TECHOTAKU182/Pilot-Light/enclosure/previews/dimensions.png

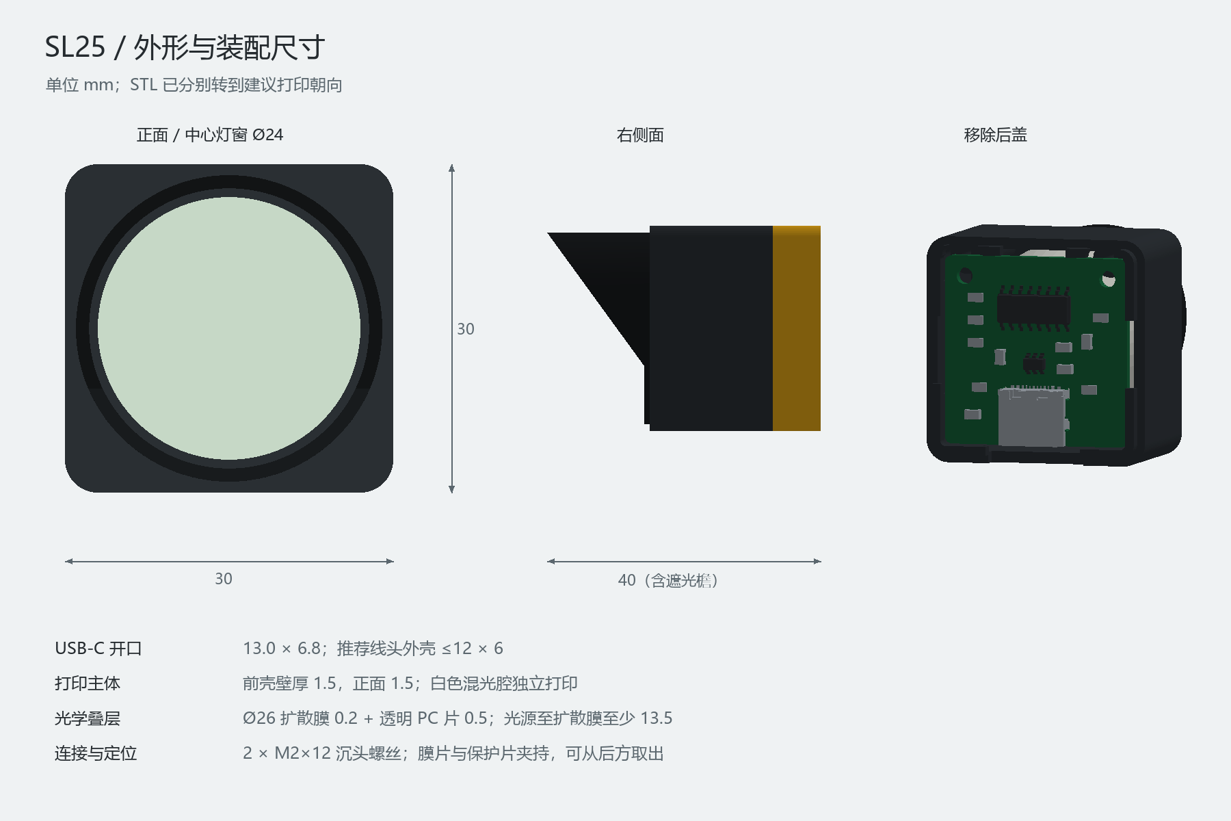
enclosure/previews/dimensions.png
