TECHOTAKU182/Pilot-Light/enclosure/previews/hood_profile.png

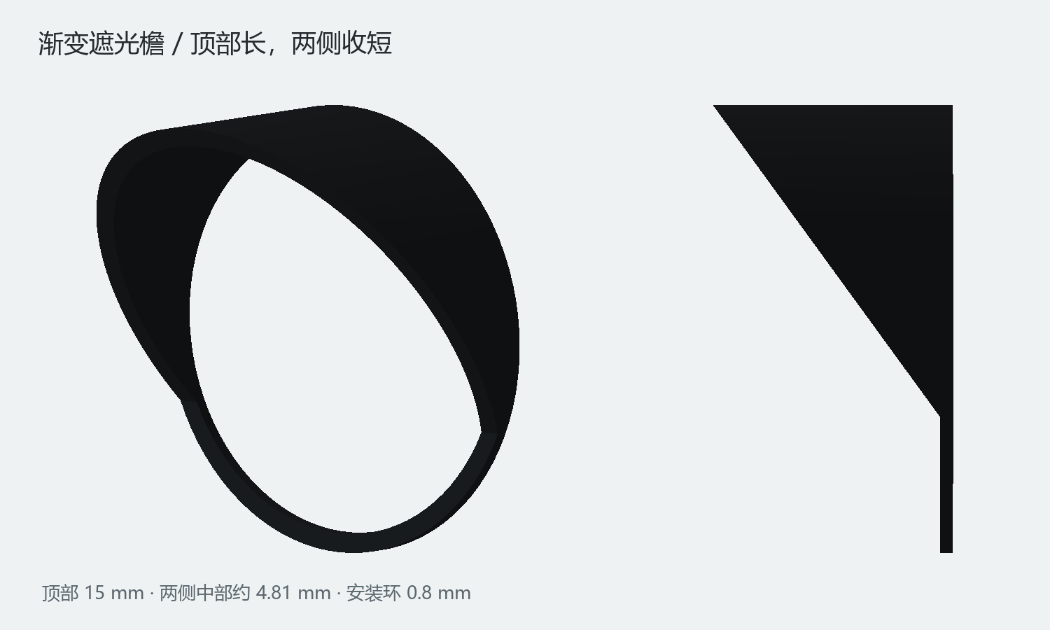
enclosure/previews/hood_profile.png
