TECHOTAKU182/Pilot-Light/enclosure/sl25_traffic/preview/color_states.png

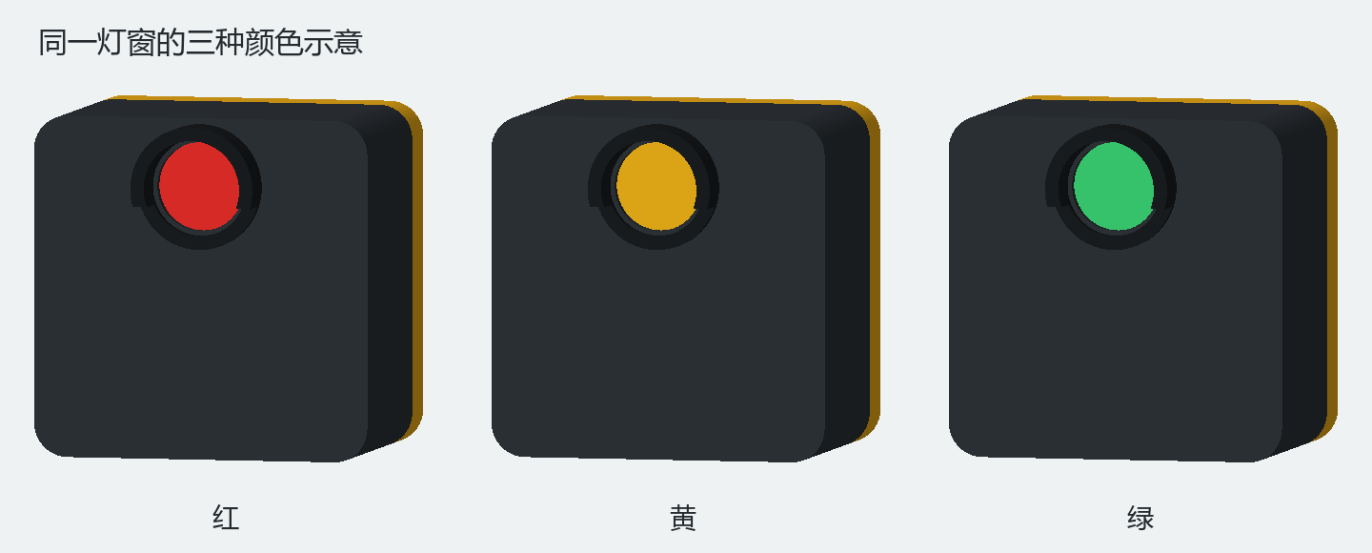
enclosure/sl25_traffic/preview/color_states.png
