TECHOTAKU182/Pilot-Light/enclosure/sl25_traffic/preview/dimensions.png

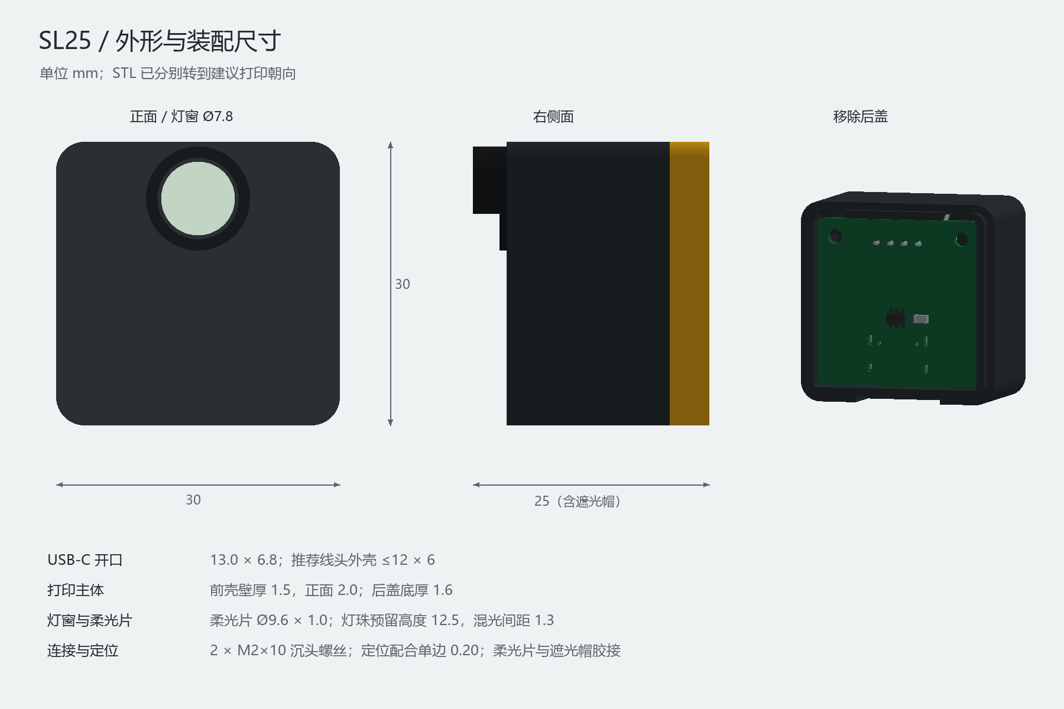
enclosure/sl25_traffic/preview/dimensions.png
