TECHOTAKU182/Pilot-Light/enclosure/sl25_traffic/preview/usb_underside.png

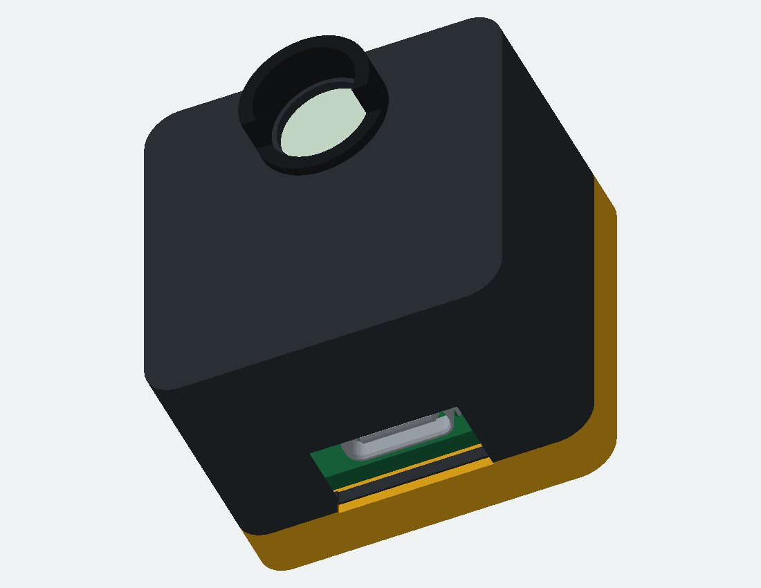
enclosure/sl25_traffic/preview/usb_underside.png
