TECHOTAKU182/Pilot-Light/enclosure/sl25_traffic_rev_b/preview/color_states.png

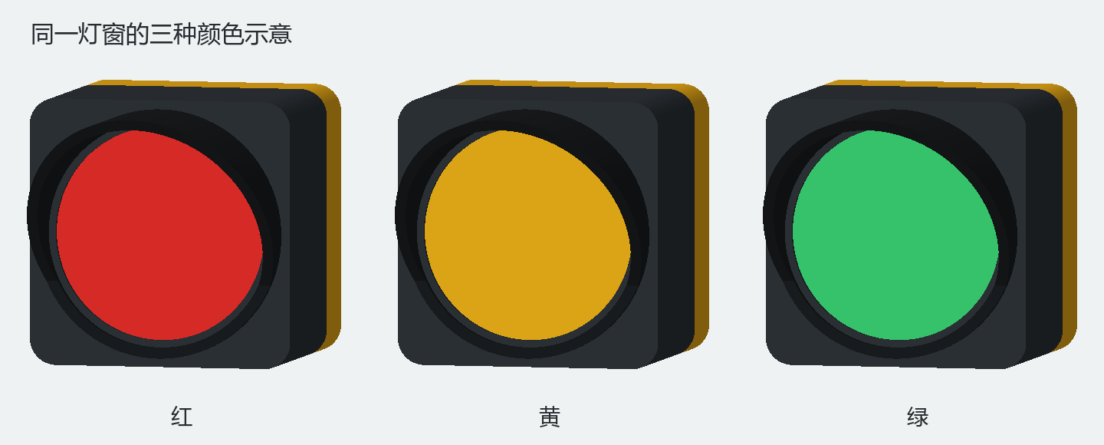
enclosure/sl25_traffic_rev_b/preview/color_states.png
