TECHOTAKU182/Pilot-Light/enclosure/sl25_traffic_rev_b/preview/usb_underside.png

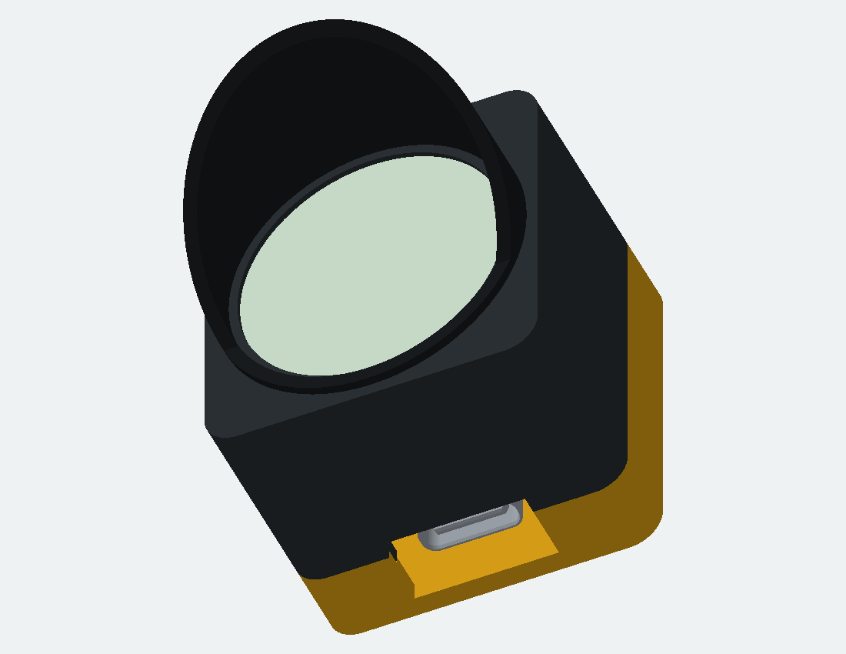
enclosure/sl25_traffic_rev_b/preview/usb_underside.png
