TECHOTAKU182/Pilot-Light/hardware/reference/LED-pinout.png

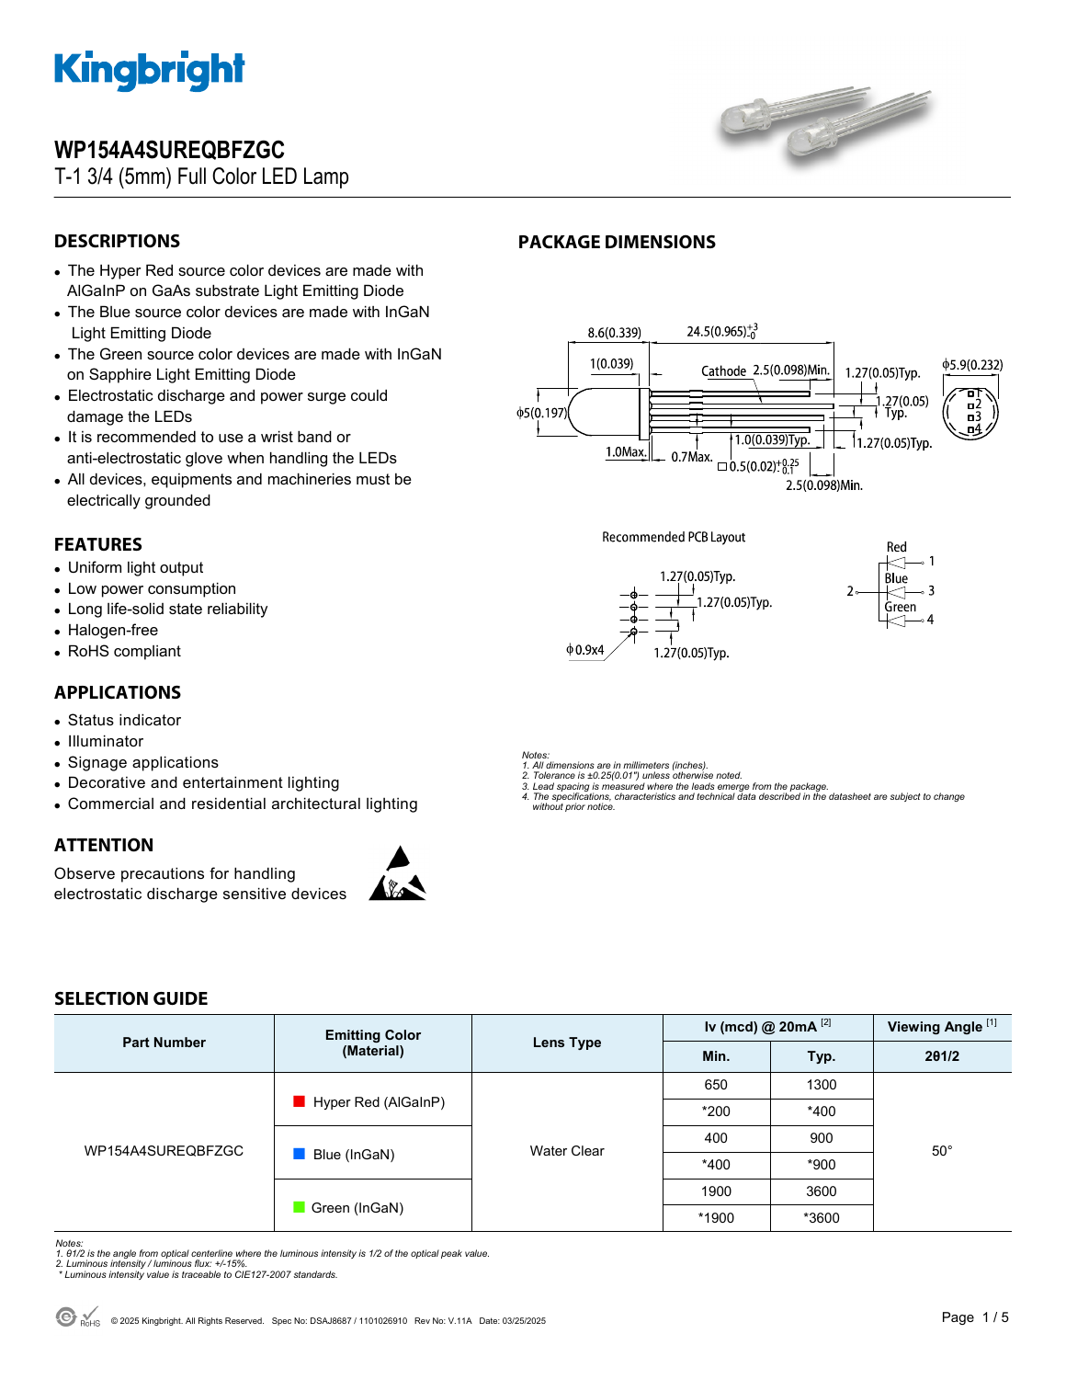
hardware/reference/LED-pinout.png
