TECHOTAKU182/Pilot-Light/hardware/reference/USB4105-drawing.png

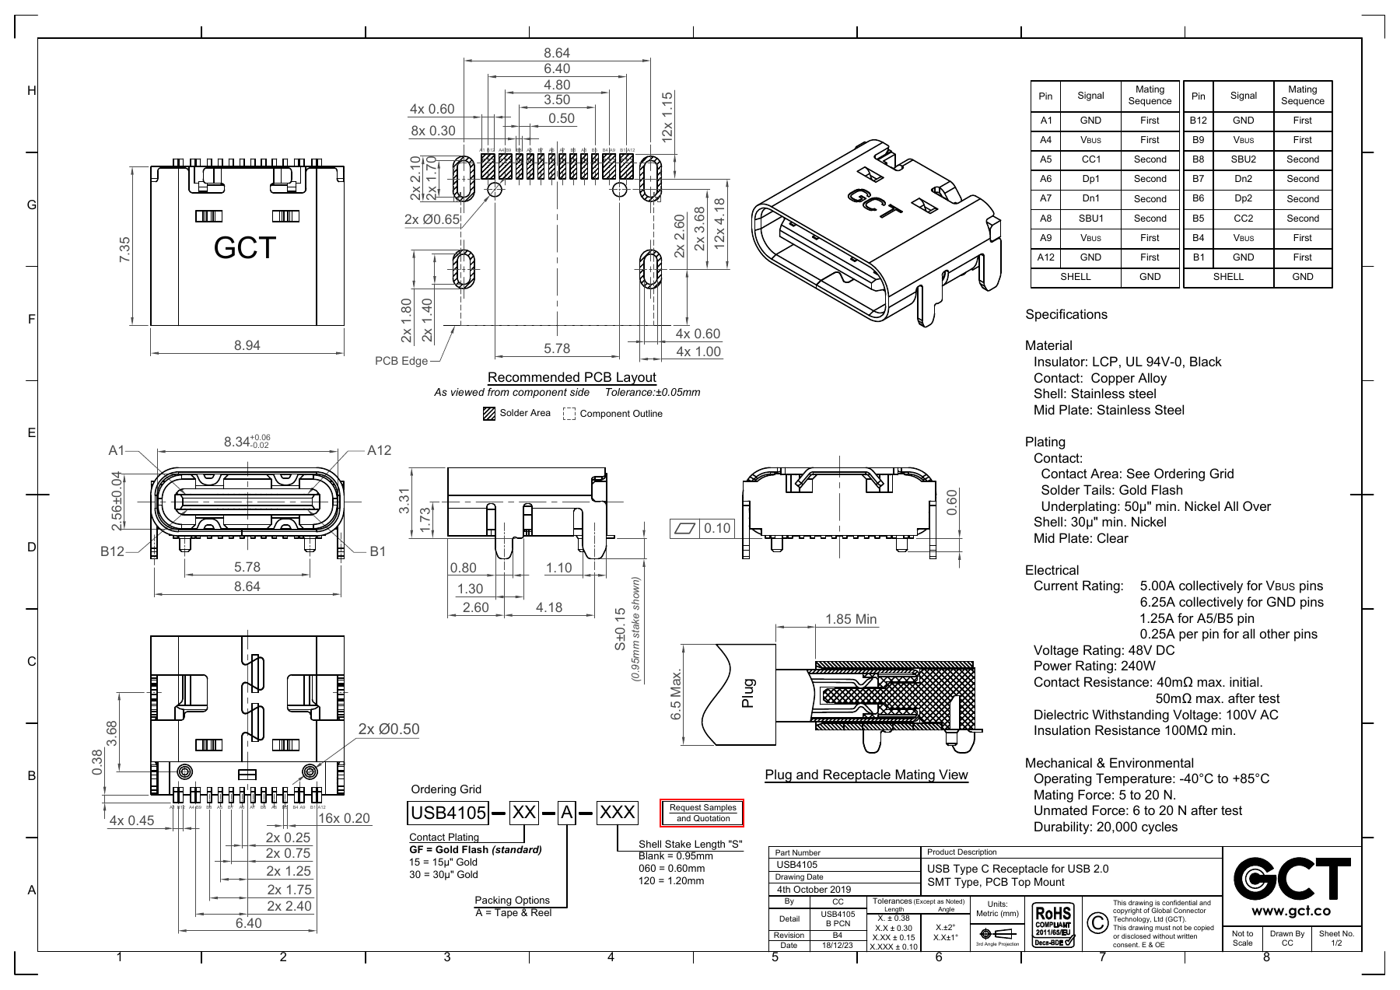
hardware/reference/USB4105-drawing.png
