TECHOTAKU182/Pilot-Light/hardware/reference/WS2812B-pinout.png

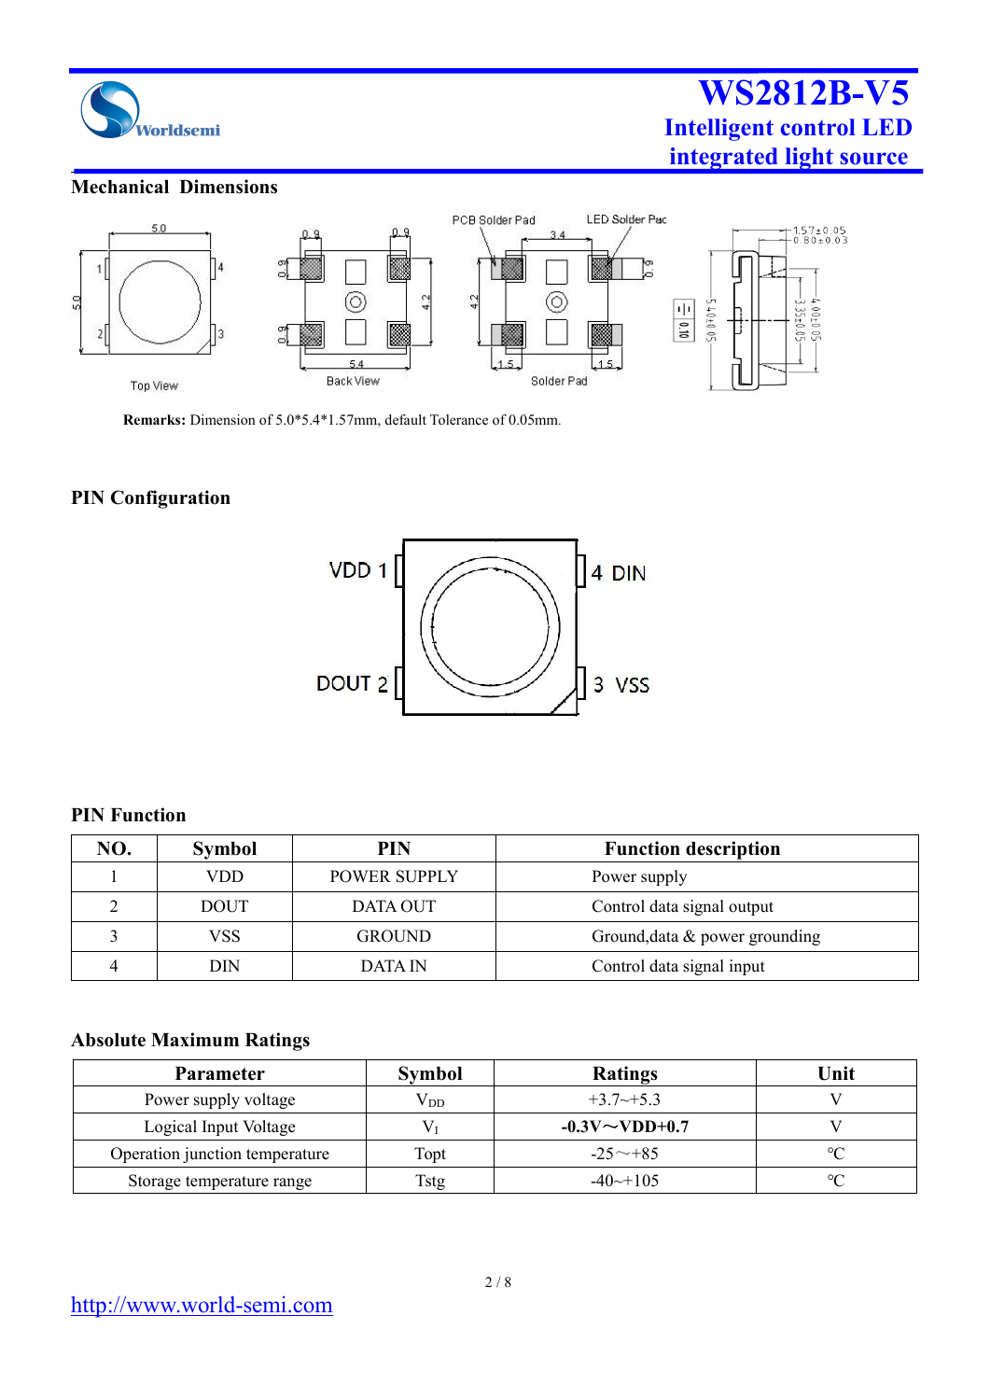
hardware/reference/WS2812B-pinout.png
