TECHOTAKU182/Pilot-Light/hardware/sl25/preview/board-top.png

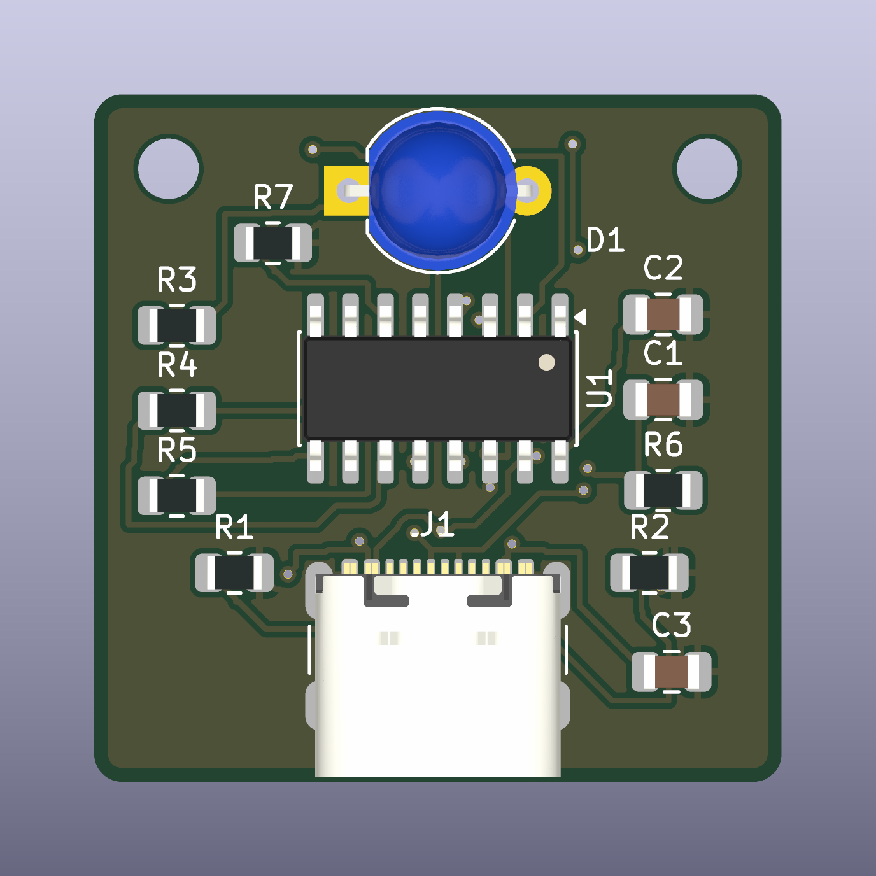
hardware/sl25/preview/board-top.png
