TECHOTAKU182/Pilot-Light/SL25-RevB/enclosure/sl25_traffic_rev_b/preview/hood_profile.png

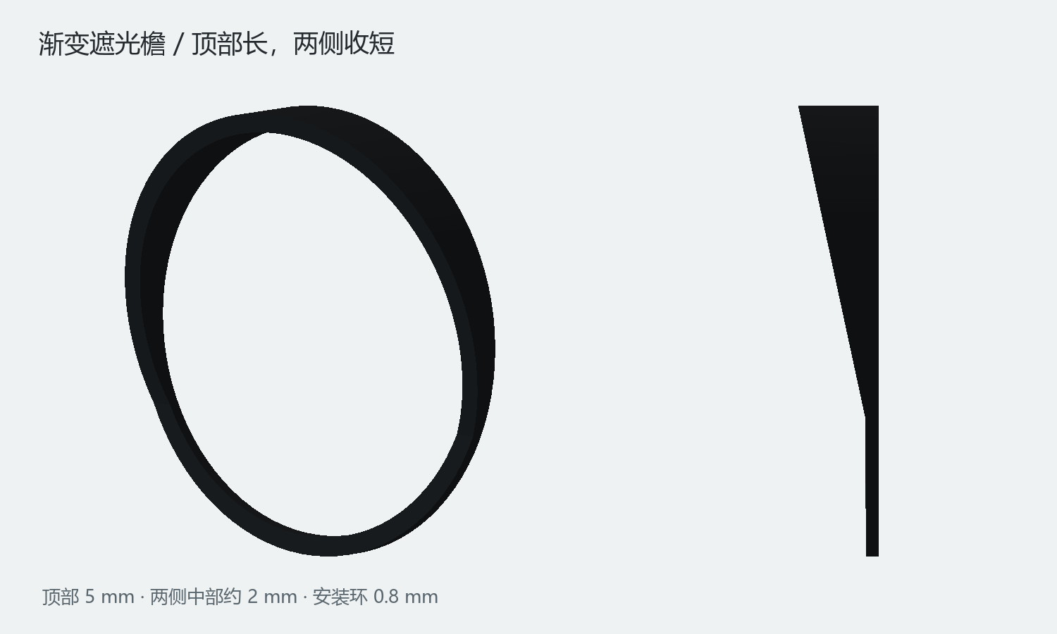
SL25-RevB/enclosure/sl25_traffic_rev_b/preview/hood_profile.png
