TECHOTAKU182/Pilot-Light/SL25-RevB/enclosure/sl25_traffic_rev_b/preview/usb_underside.png

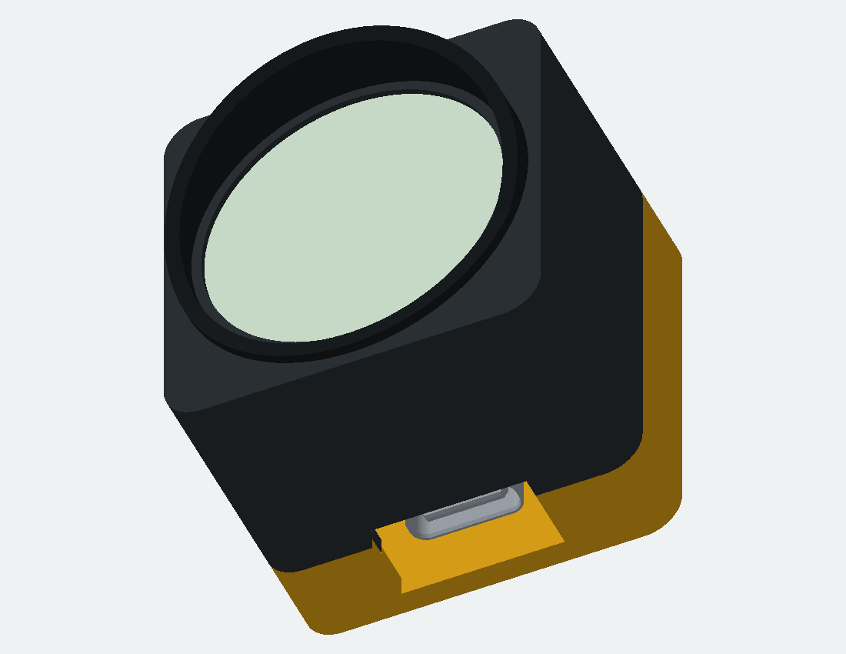
SL25-RevB/enclosure/sl25_traffic_rev_b/preview/usb_underside.png
