TECHOTAKU182/Pilot-Light/hardware/sl25/models/USB_C_Receptacle_GCT_USB4105-xx-A_16P_TopMnt_Horizontal.step

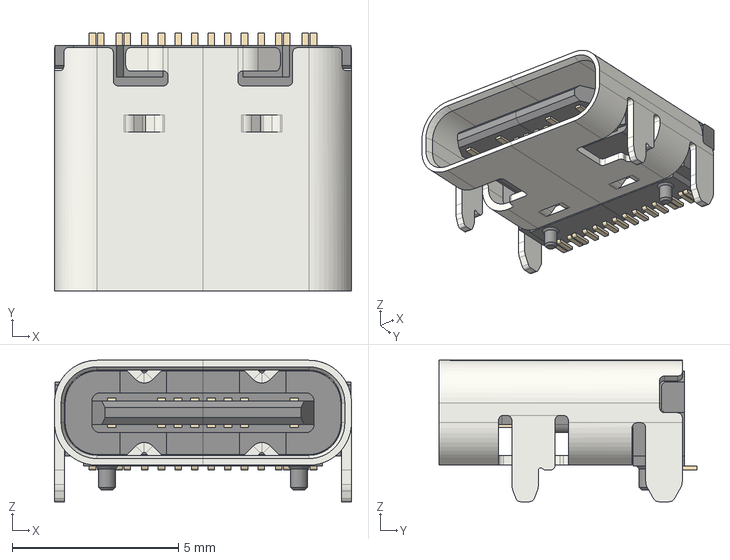
[picture p36: CAD file, 2026-09-17]
hardware/sl25/models/USB_C_Receptacle_GCT_USB4105-xx-A_16P_TopMnt_Horizontal.step
8.94 x 7.78 x 4.26 mm
