TECHOTAKU182/Pilot-Light/hardware/sl25_rev_b/models/R_0805_2012Metric.step

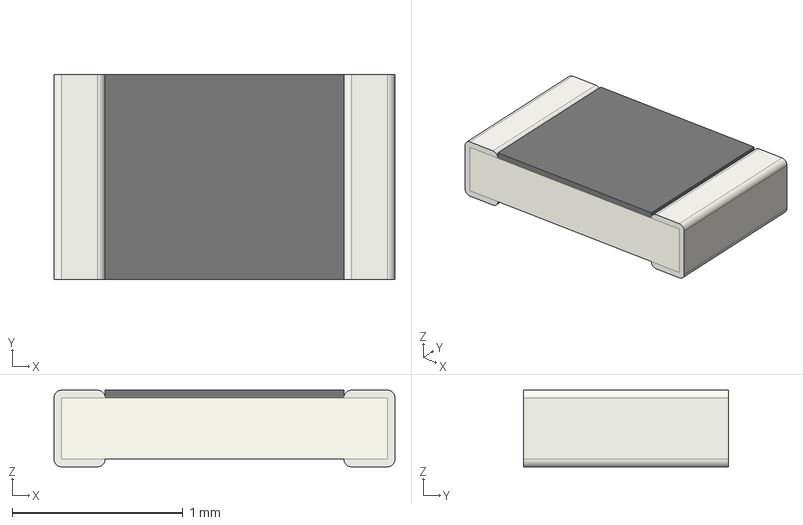
[picture p37: CAD file, 2026-09-17]
hardware/sl25_rev_b/models/R_0805_2012Metric.step
2.00 x 1.20 x 0.45 mm
