TECHOTAKU182/Pilot-Light/SL25-RevB/enclosure/sl25_traffic_rev_b/cad/01_rear_cover.step

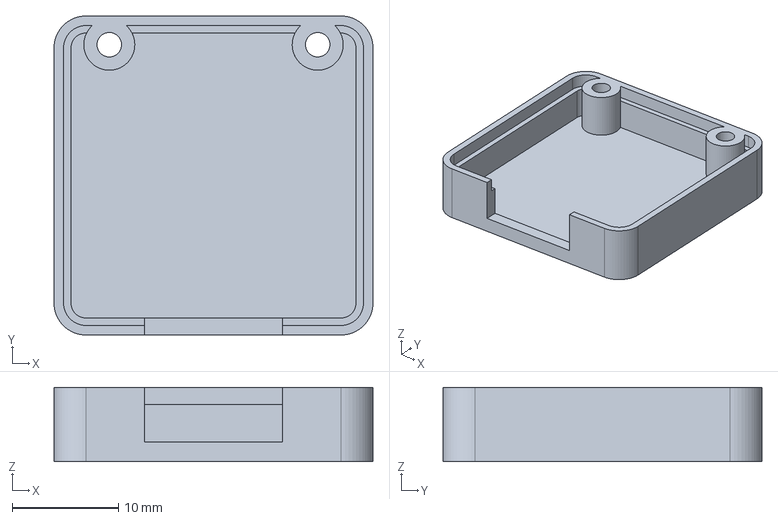
[picture p38: CAD file, 2026-09-17]
SL25-RevB/enclosure/sl25_traffic_rev_b/cad/01_rear_cover.step
30.0 x 30.0 x 7.00 mm
