TECHOTAKU182/Pilot-Light/enclosure/sl25_traffic/cad/03_signal_hood.step

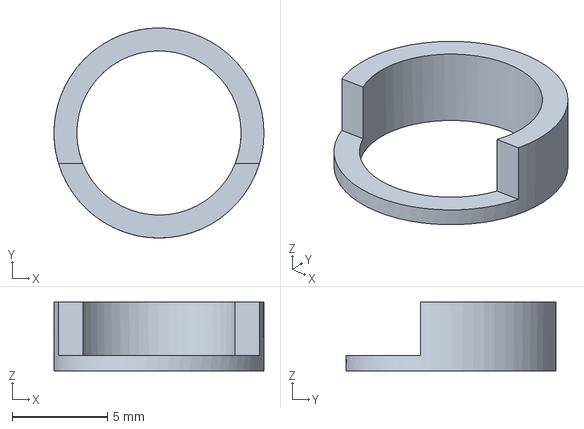
[picture p39: CAD file, 2026-09-17]
enclosure/sl25_traffic/cad/03_signal_hood.step
11.0 x 11.0 x 3.60 mm
