TECHOTAKU182/Pilot-Light/enclosure/sl25_traffic_rev_b/cad/03_signal_hood.step

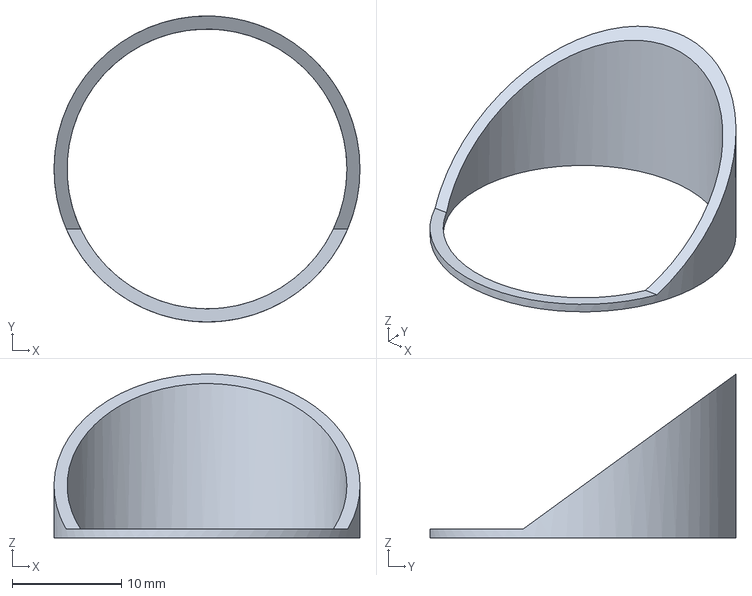
[picture p40: CAD file, 2026-09-17]
enclosure/sl25_traffic_rev_b/cad/03_signal_hood.step
28.0 x 28.0 x 15.0 mm
