TECHOTAKU182/Pilot-Light/hardware/sl25_rev_b/models/LED_WS2812B_PLCC4_5.0x5.0mm_P3.2mm.step

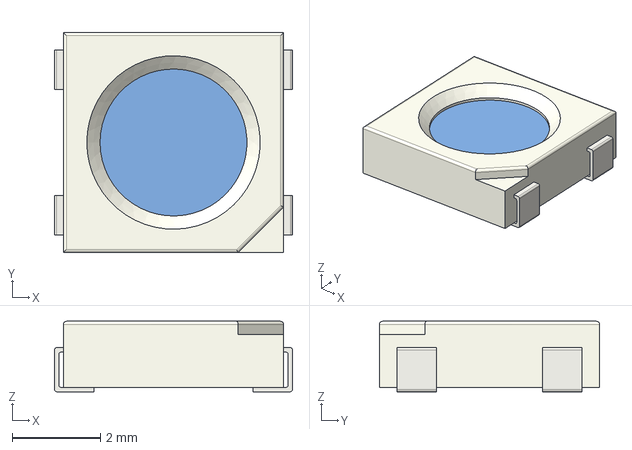
[picture p41: CAD file, 2026-09-17]
hardware/sl25_rev_b/models/LED_WS2812B_PLCC4_5.0x5.0mm_P3.2mm.step
5.40 x 5.00 x 1.60 mm
