TECHOTAKU182/Pilot-Light/SL25-RevB/hardware/sl25_rev_b/models/SOIC-16_3.9x9.9mm_P1.27mm.step

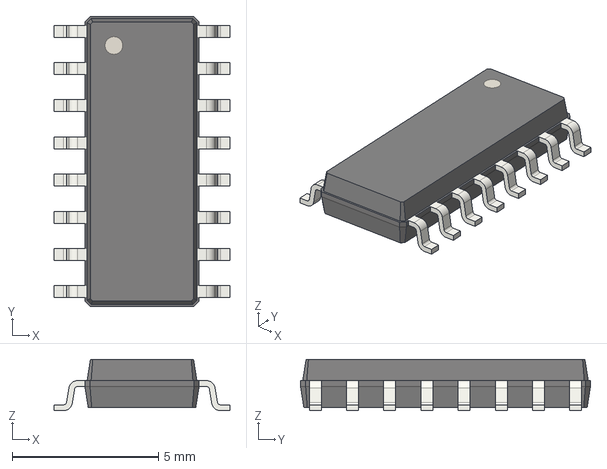
[picture p42: CAD file, 2026-09-17]
SL25-RevB/hardware/sl25_rev_b/models/SOIC-16_3.9x9.9mm_P1.27mm.step
6.00 x 9.90 x 1.75 mm
