TECHOTAKU182/Pilot-Light/enclosure/sl25_traffic/cad/02_front_housing.step

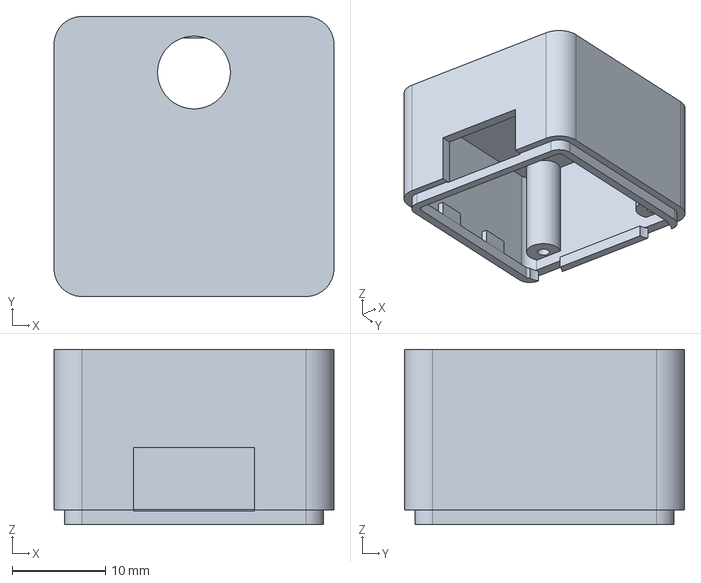
[picture p43: CAD file, 2026-09-17]
enclosure/sl25_traffic/cad/02_front_housing.step
30.0 x 30.0 x 18.8 mm
