TECHOTAKU182/Pilot-Light/enclosure/sl25_traffic_rev_b/cad/06_clear_protector.step

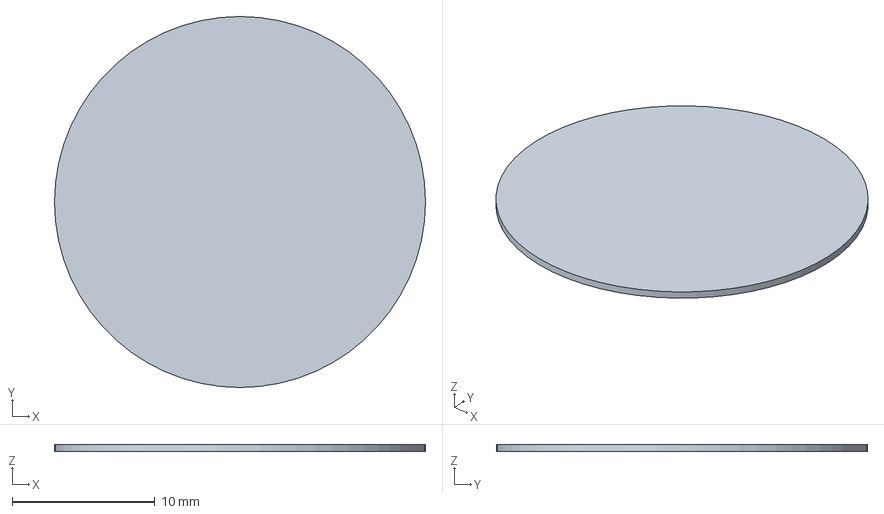
[picture p44: CAD file, 2026-09-17]
enclosure/sl25_traffic_rev_b/cad/06_clear_protector.step
26.0 x 26.0 x 0.5 mm
