TECHOTAKU182/Pilot-Light/SL25-RevB/enclosure/sl25_traffic_rev_b/cad/03_signal_hood.step

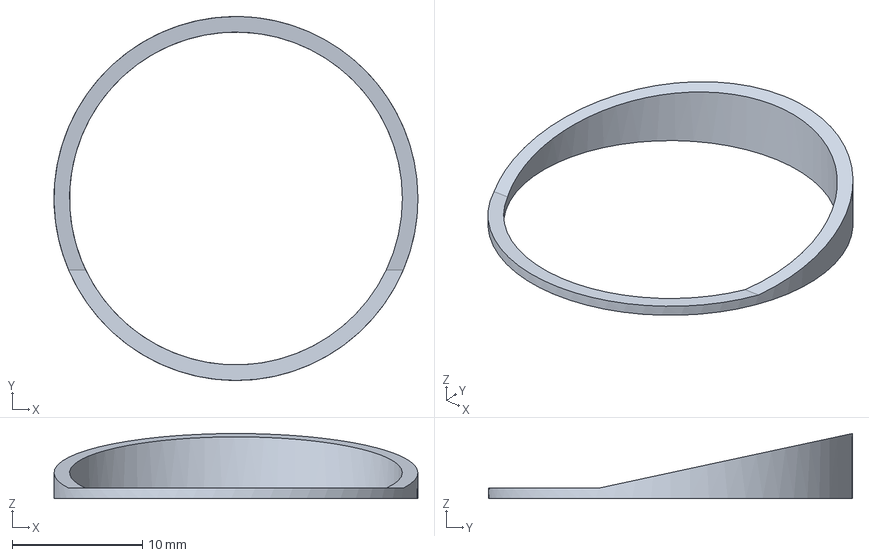
[picture p45: CAD file, 2026-09-17]
SL25-RevB/enclosure/sl25_traffic_rev_b/cad/03_signal_hood.step
28.0 x 28.0 x 5.00 mm
