TECHOTAKU182/Pilot-Light/enclosure/sl25_traffic/preview/assembly.png

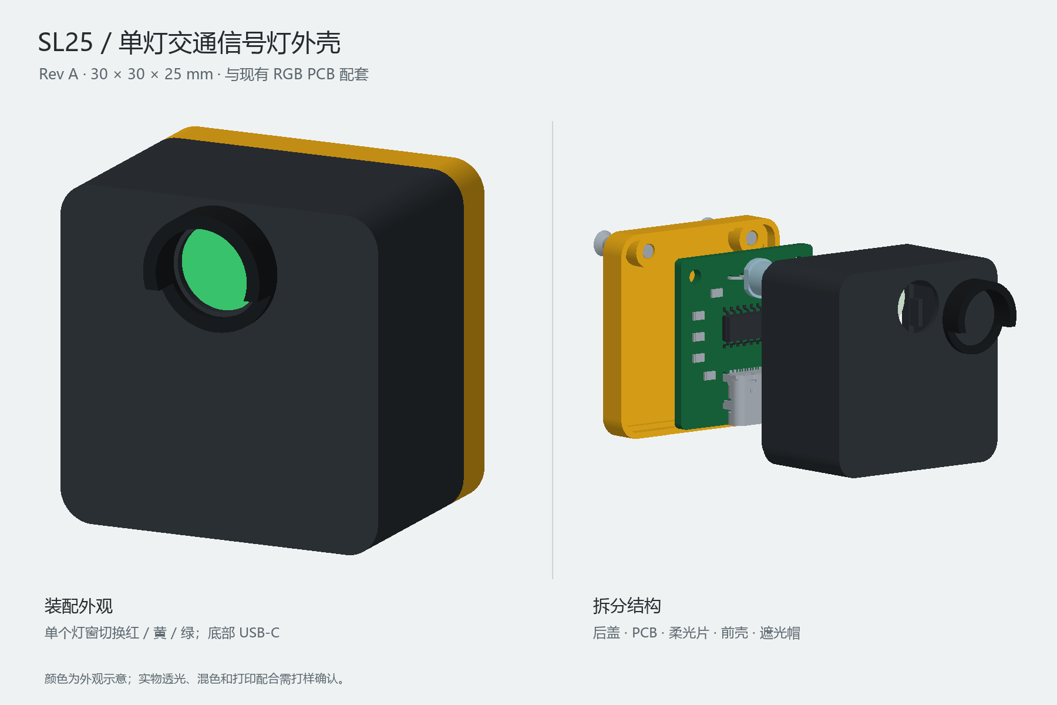
enclosure/sl25_traffic/preview/assembly.png
